osresearch/model100/verilog/spi_device.v

`ifndef _spi_device_v_
`define _spi_device_v_

/**
 * SPI device clocked in the spi_clk domain.
 *
 * Outputs are unregistered so that they can be processed on the
 * rising edge of the 8th bit, allowing new data to be available
 * before the falling edge of the next spi_clk.
 */

module spi_device(
	input	spi_clk,
	input	spi_cs,
	input	spi_mosi,
	output	spi_miso,
	output	spi_rx_strobe,
	output [7:0] spi_rx_data,
	input 	spi_tx_ready,
	input [7:0] spi_tx_data
);
	reg [2:0]     bit_count;
	reg [7:0]     mosi_reg;

	// these are unlatched so that they are available immediately
	assign spi_rx_strobe = bit_count == 7;
	assign spi_rx_data = { mosi_reg[6:0], spi_mosi };

	always @(posedge spi_clk or posedge spi_cs)
	begin
		if (spi_cs) begin
			// anytime the spi_cs goes high, reset the bit count
			bit_count <= 0;
		end else
		begin
			// shift in the rx data on the rising edge
			bit_count <= bit_count + 1;
			mosi_reg <= spi_rx_data;
		end
	end

	always @(negedge spi_clk) begin
		// shift out the tx data on the falling edge
		spi_miso <= spi_tx_data[7-bit_count];
	end
endmodule

`endif
